killerzman/OrCAD-AudioPowerAmplifier/Schematics/Amplificator audio de putere-PSpiceFiles/SCHEMATIC1/Amplificator audio de putere/Draft1.asc

R1: res; 1k
R2: res; 1k
R3: res; 1k
R4: res; 1k
U1: LT1001
V1: voltage; SINE(0 1 1k)
V2: voltage; PWL(0 -1 0.5m -1 0.501m 1 1m 1 1.001m -1 1.5m -1 1.501m -1 1.501m 1 2ms 1 2.001m -1 2.5m -1)
Named nets: 0, VDD, VSS
.tran 0 2.5m 0 0.1u
